skiselev/micro_8088/KiCad/8088-FE2010A-SBC-Board-1.1.pdf

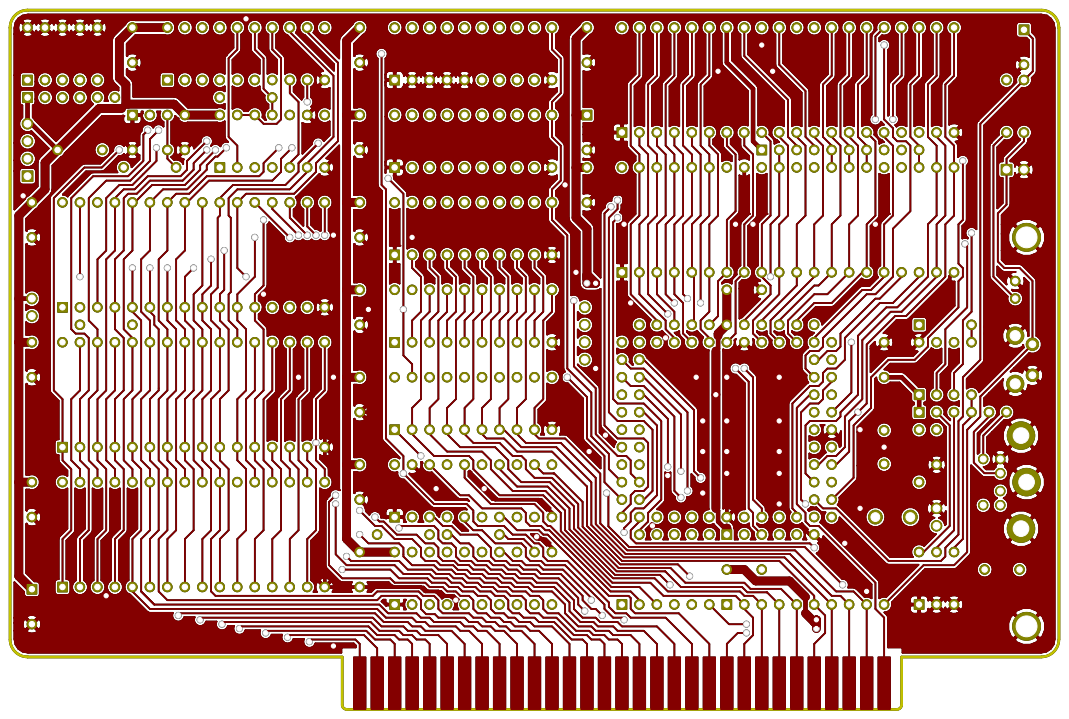
[picture p13: page 1]

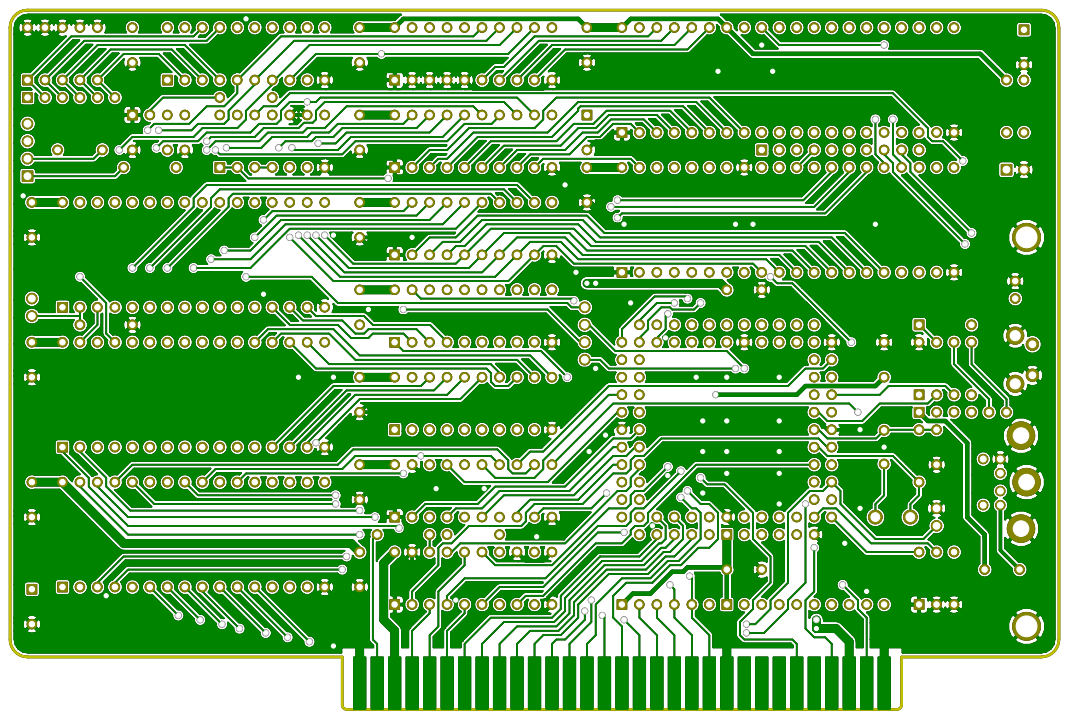
[picture p14: page 2]

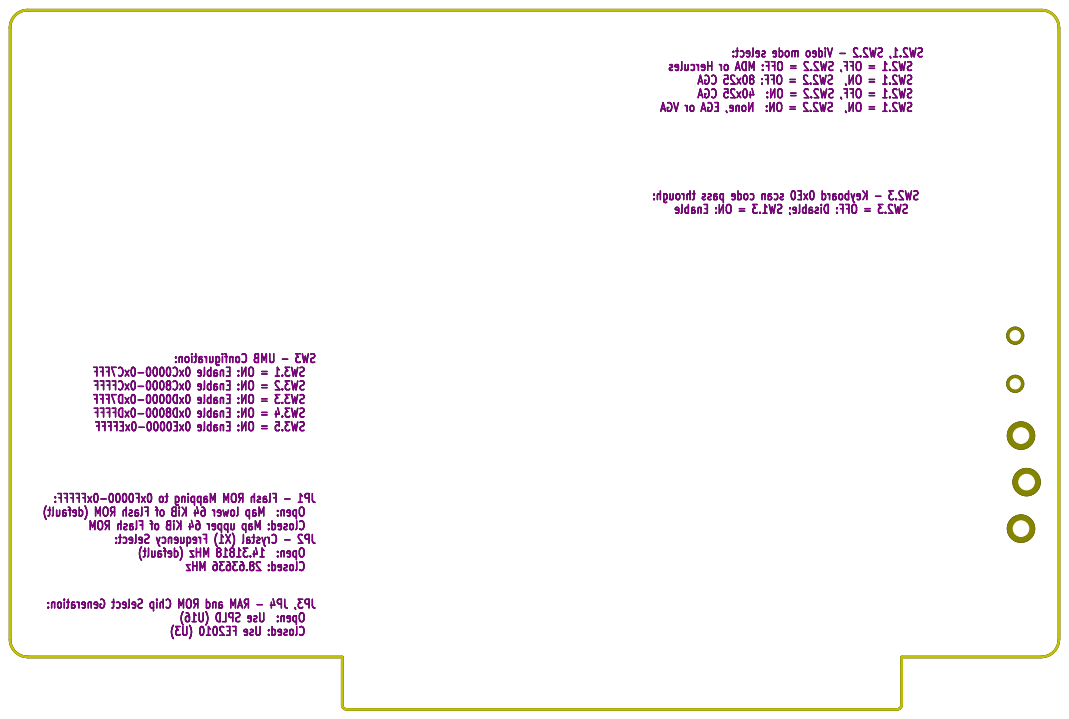
[picture p15: page 3]

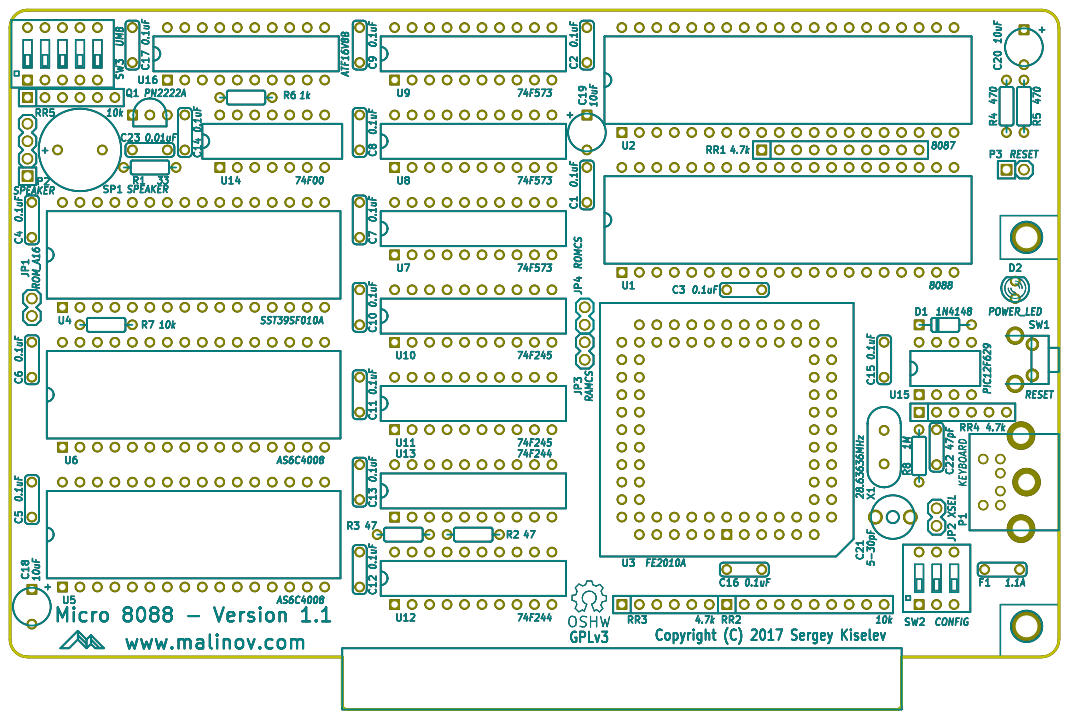
[picture p16: page 4]
