skiselev/micro_8088/KiCad/8088-FE2010A-SBC-Board-1.0.pdf

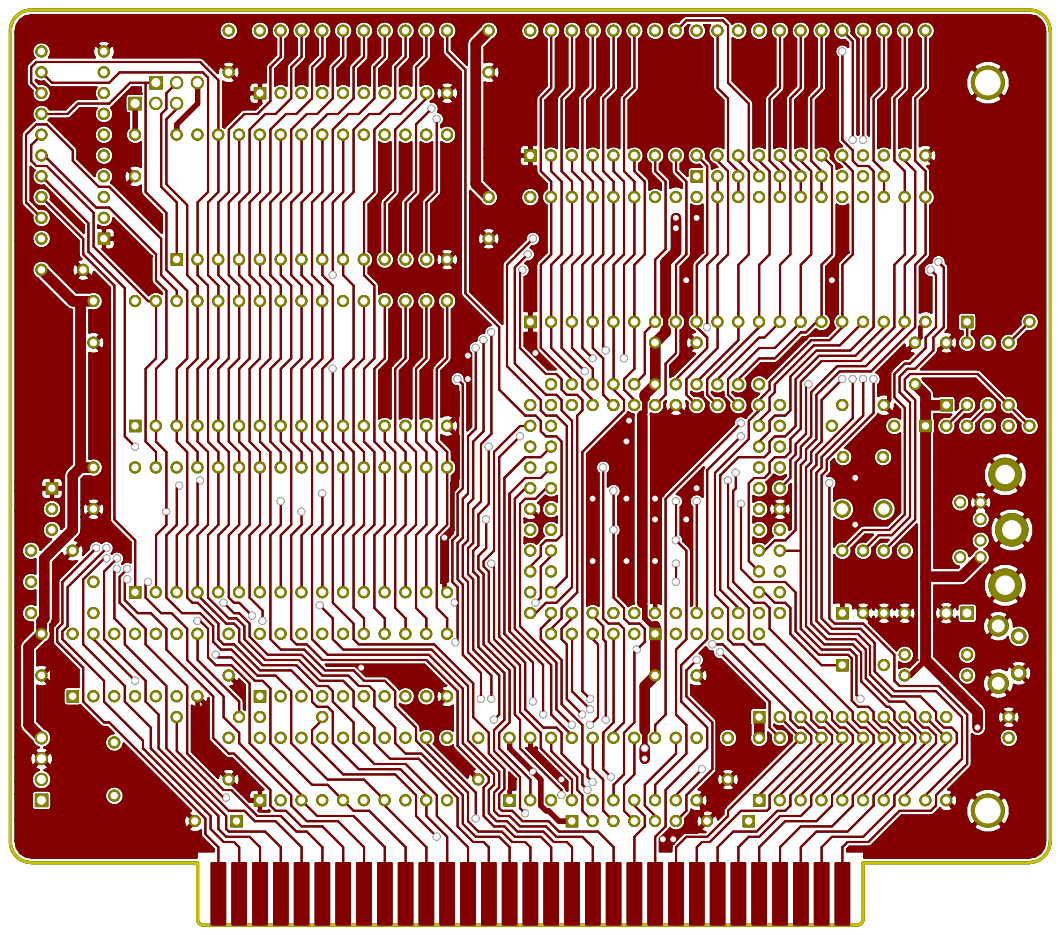
[picture p17: page 1]

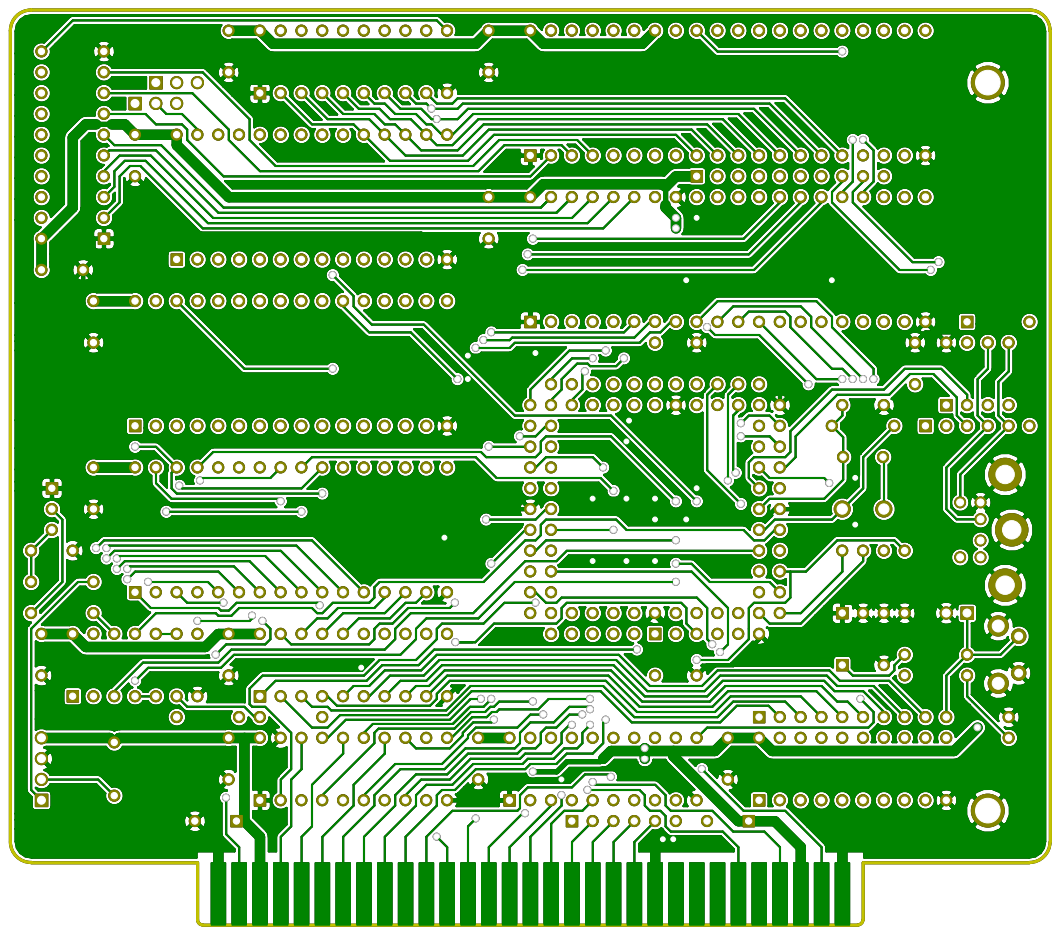
[picture p18: page 2]

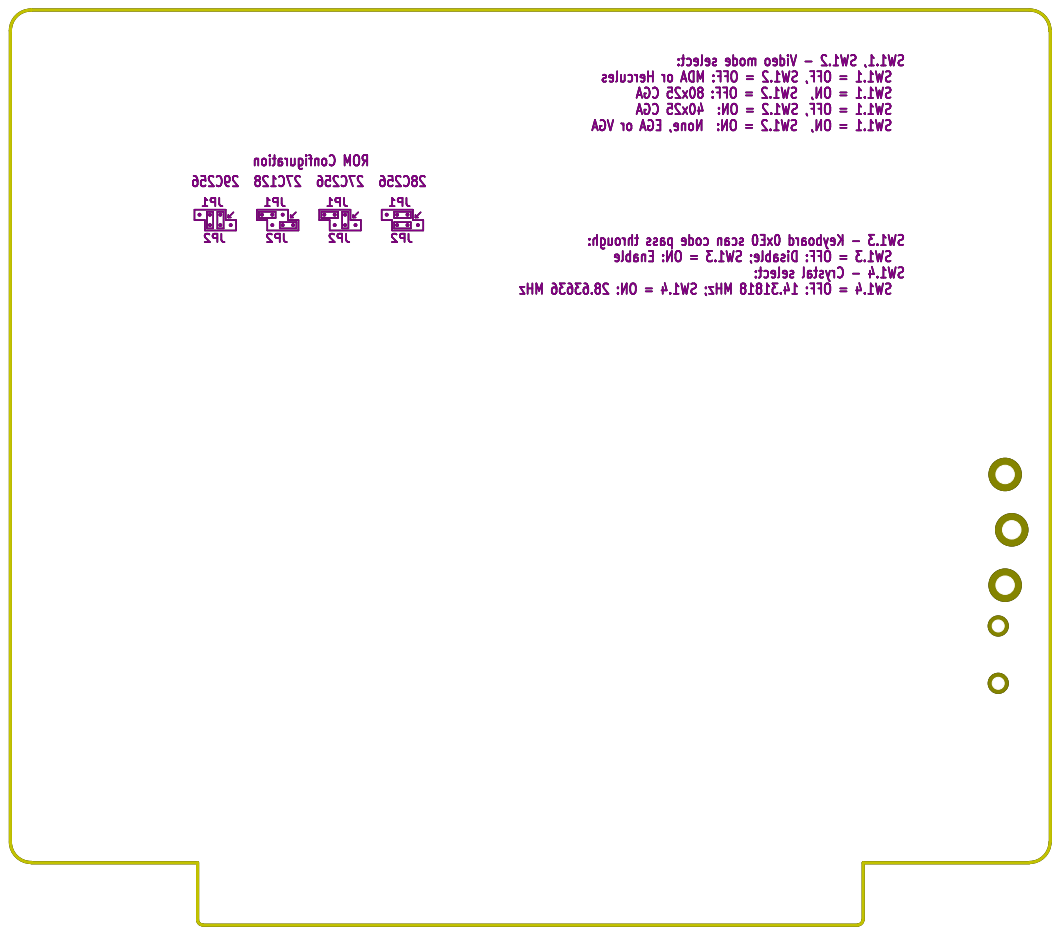
[picture p19: page 3]

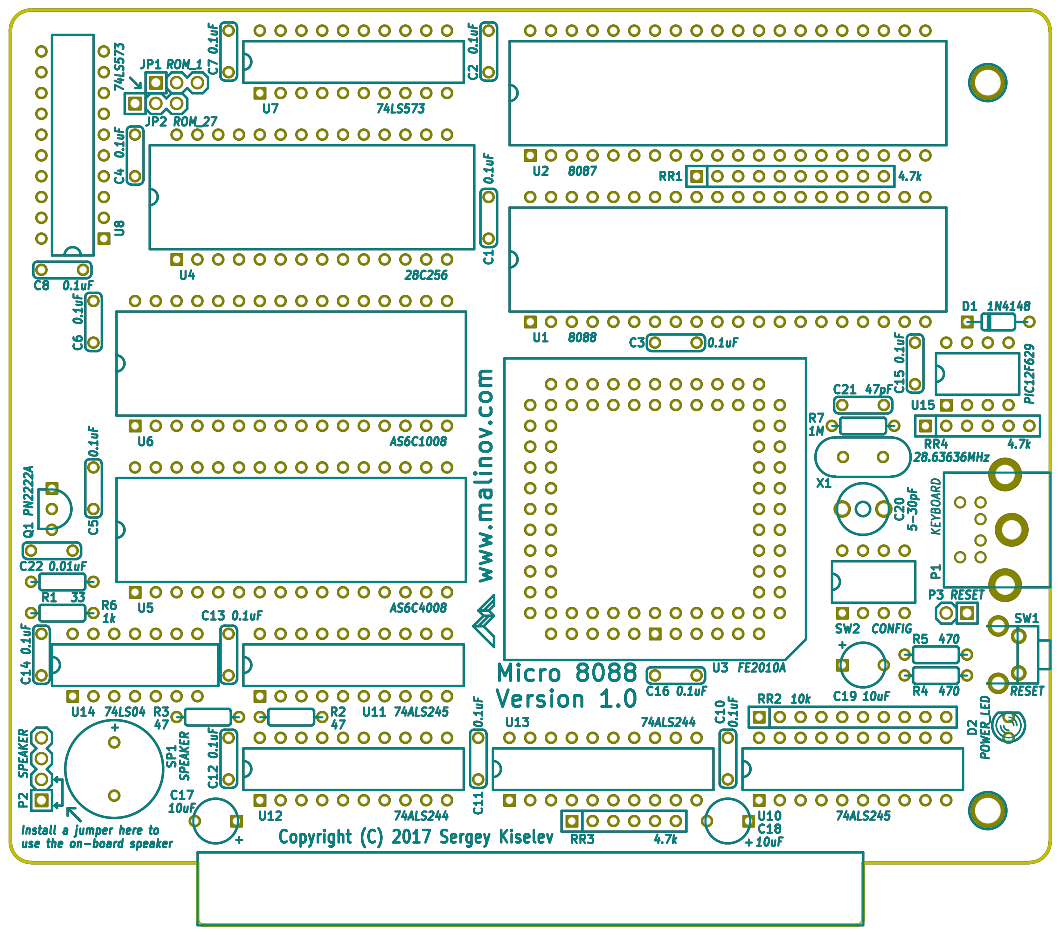
[picture p20: page 4]
